EJ-JATIMohammed/stm32-RedBoard/PCB_images/5.png

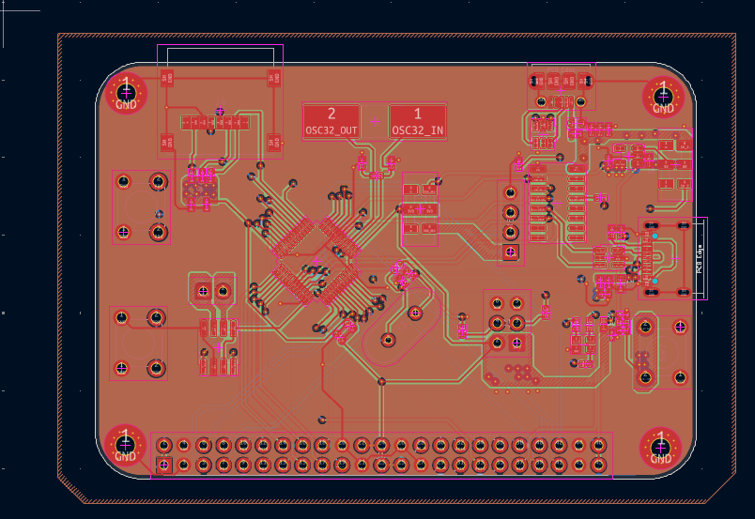
PCB_images/5.png
