EJ-JATIMohammed/stm32-RedBoard/PCB_images/6.png

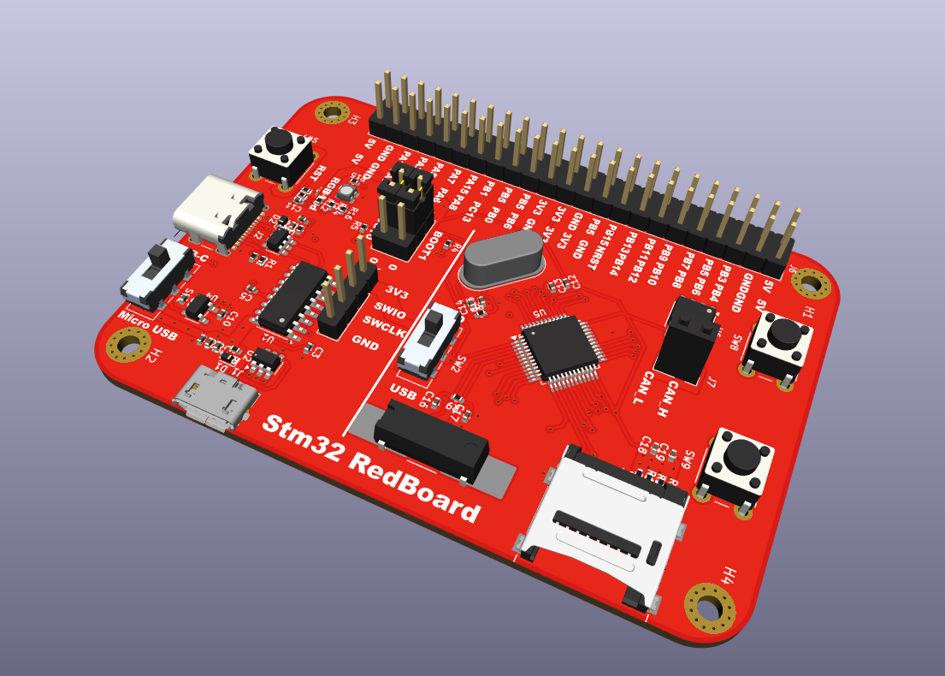
PCB_images/6.png
