EJ-JATIMohammed/stm32-RedBoard/PCB_images/7.png

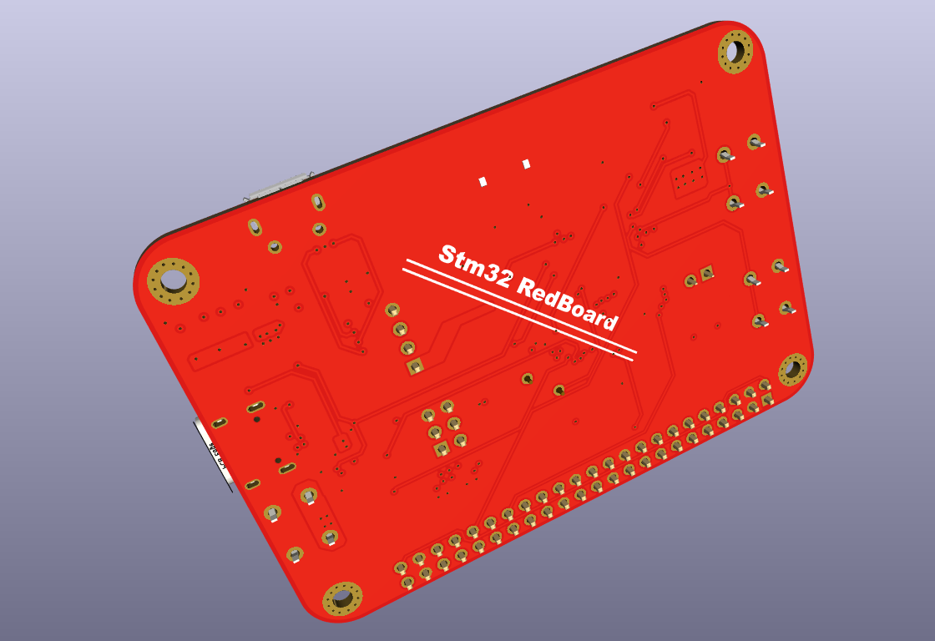
PCB_images/7.png
